MrBoggi/3d-boats/projects/01-21ft-rib/image.png

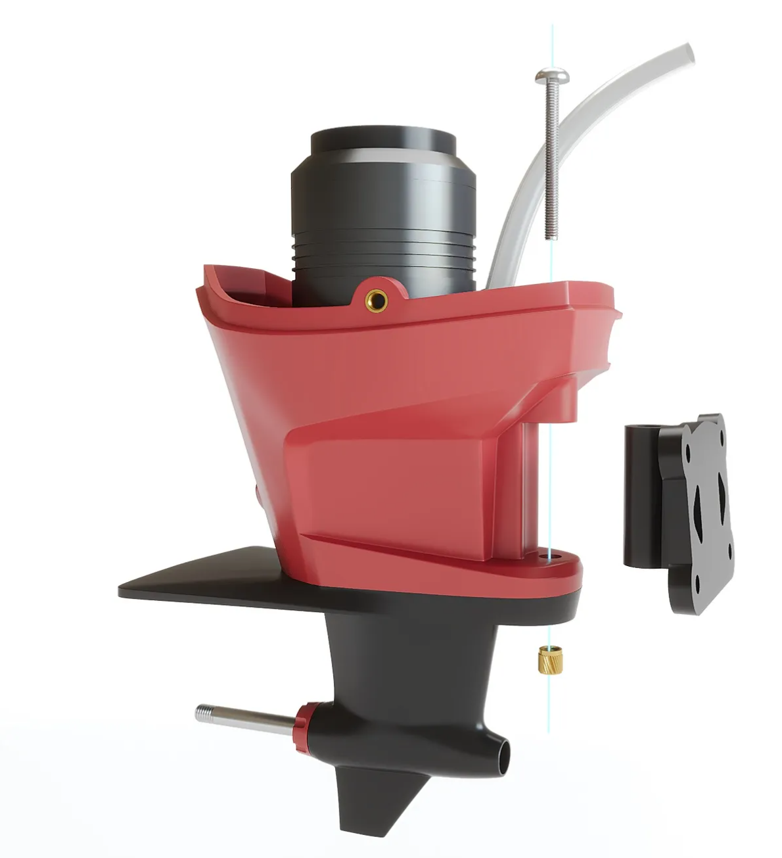
projects/01-21ft-rib/image.png
