MrBoggi/3d-boats/projects/02-21ft-rib-trailer/png/review_bogie_travel.png

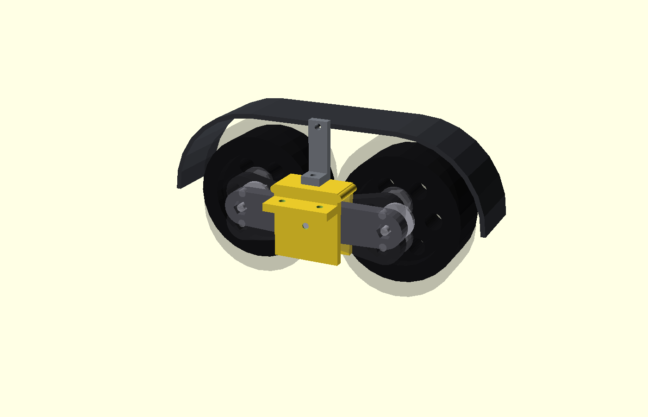
projects/02-21ft-rib-trailer/png/review_bogie_travel.png
