MrBoggi/3d-boats/projects/02-21ft-rib-trailer/png/review_bow_stop_pivot.png

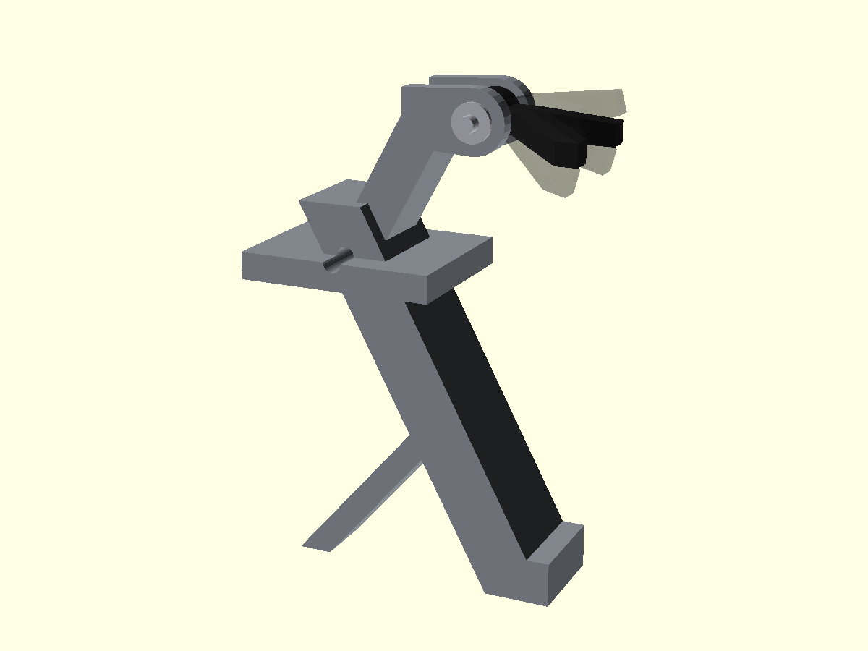
projects/02-21ft-rib-trailer/png/review_bow_stop_pivot.png
