MrBoggi/3d-boats/projects/02-21ft-rib-trailer/png/review_service_rear.png

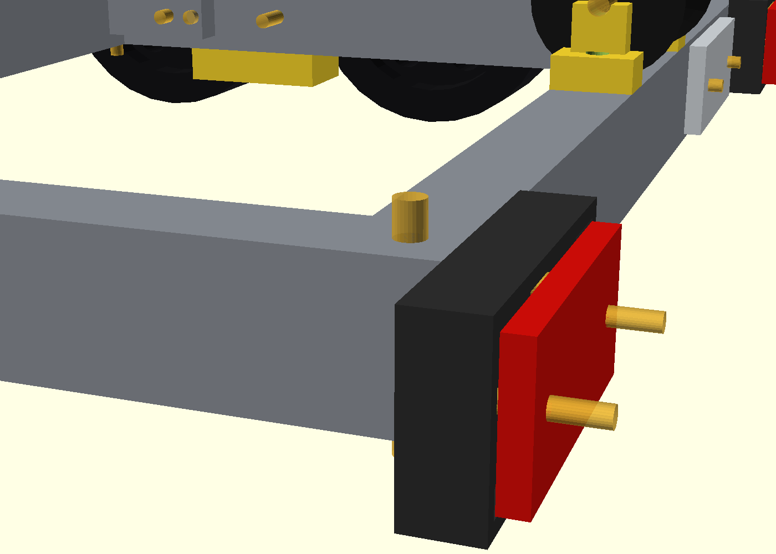
projects/02-21ft-rib-trailer/png/review_service_rear.png
