MrBoggi/3d-boats/projects/02-21ft-rib-trailer/3mf/plates/trailer_petg_plate_04.3mf

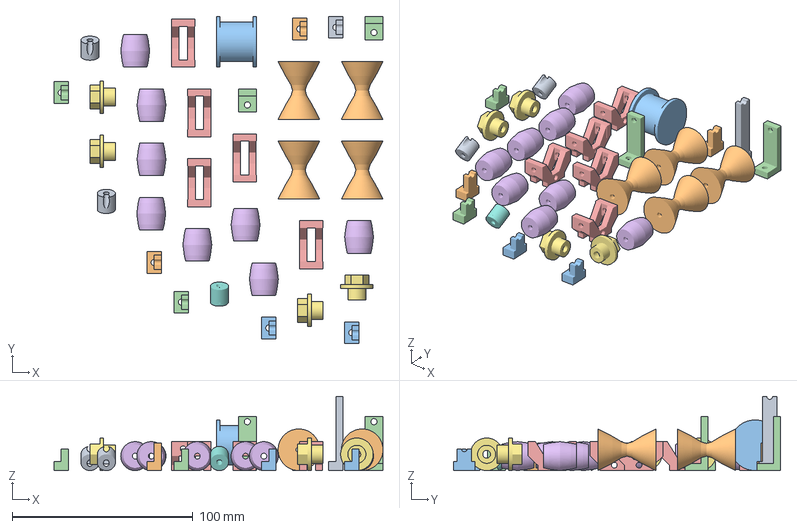
[picture p26: CAD file, 2026-08-22]
projects/02-21ft-rib-trailer/3mf/plates/trailer_petg_plate_04.3mf
181.9 x 180.8 x 41.0 mm
keel_roller_bracket_front.stl
keel_roller.stl x 4
winch_drum.stl
fender_mount_bracket.stl x 2
side_roller_wobble_holder.stl x 5
side_support_roller.stl x 8
wheel_hex_adapter.stl x 4
side_support_post_rear.stl
side_support_post_front.stl x 2
keel_roller_bracket_mid_front.stl x 2
keel_roller_bracket_mid_rear.stl x 2
keel_roller_bracket_rear.stl x 2
