MrBoggi/3d-boats/projects/02-21ft-rib-trailer/3mf/v_rail_joint_plate.3mf

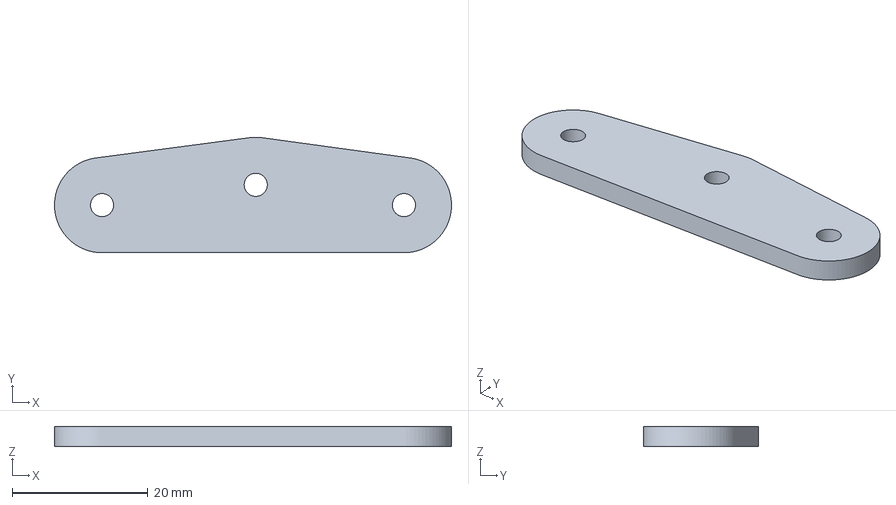
[picture p27: CAD file, 2026-08-17]
projects/02-21ft-rib-trailer/3mf/v_rail_joint_plate.3mf
58.4 x 17.0 x 3.00 mm
