MrBoggi/3d-boats/projects/01-21ft-rib/stl/bow_rail_port.stl

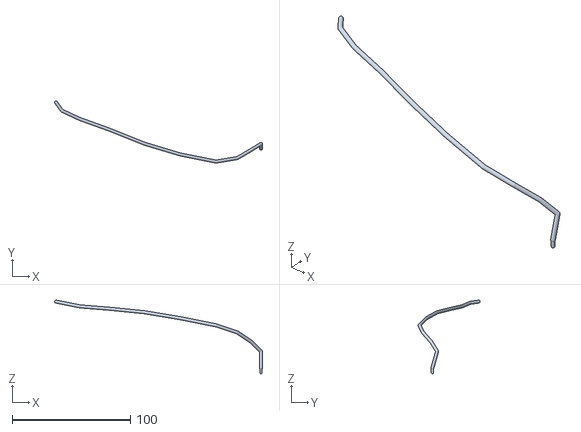
[picture p28: CAD file, 2026-08-11]
projects/01-21ft-rib/stl/bow_rail_port.stl
175.6 x 52.6 x 62.3
