MrBoggi/3d-boats/projects/02-21ft-rib-trailer/3mf/frame_rail_rear.3mf

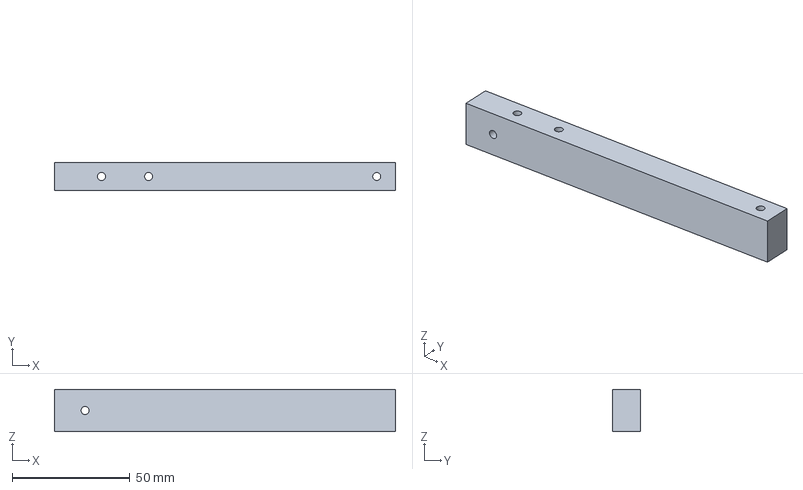
[picture p30: CAD file, 2026-08-17]
projects/02-21ft-rib-trailer/3mf/frame_rail_rear.3mf
145.0 x 12.0 x 18.0 mm
