MrBoggi/3d-boats/projects/01-21ft-rib/stl/floor_aft_lid.stl

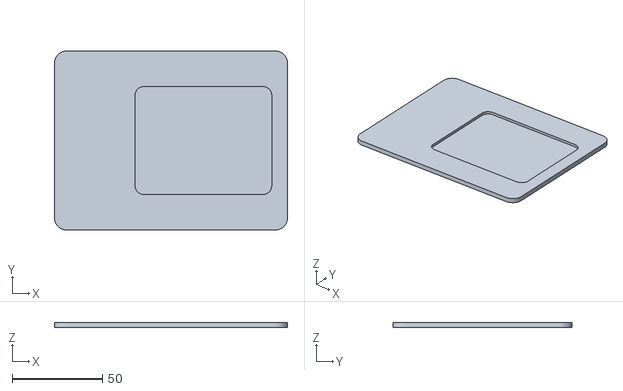
[picture p31: CAD file, 2026-08-11]
projects/01-21ft-rib/stl/floor_aft_lid.stl
129.4 x 99.4 x 3.00
