MrBoggi/3d-boats/projects/02-21ft-rib-trailer/3mf/plates/trailer_petg_plate_01.3mf

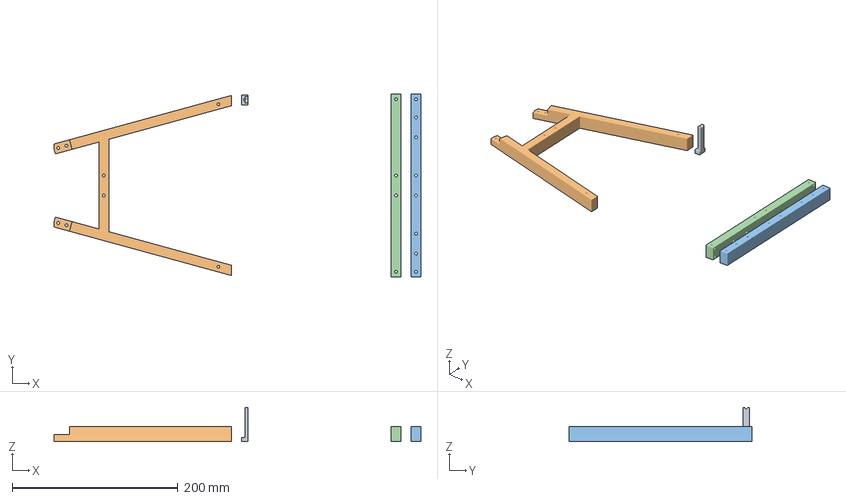
[picture p33: CAD file, 2026-08-22]
projects/02-21ft-rib-trailer/3mf/plates/trailer_petg_plate_01.3mf
442.2 x 220.0 x 41.0 mm
keel_roller_bracket_front.stl
drawbar_rear.stl
crossmember.stl
rear_accessory_crossmember.stl
