MrBoggi/3d-boats/projects/02-21ft-rib-trailer/3mf/rear_light_housing.3mf

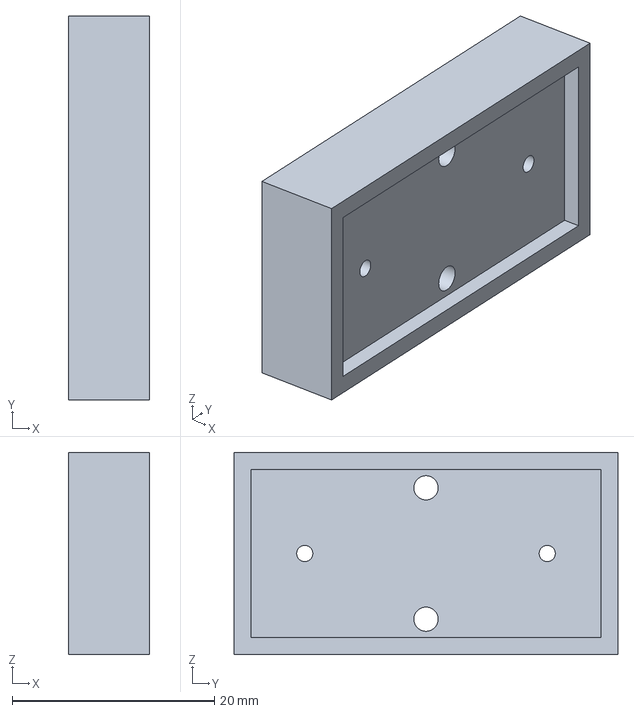
[picture p34: CAD file, 2026-08-17]
projects/02-21ft-rib-trailer/3mf/rear_light_housing.3mf
8.00 x 38.0 x 20.0 mm
