MrBoggi/3d-boats/projects/01-21ft-rib/stl/hull_mid.stl

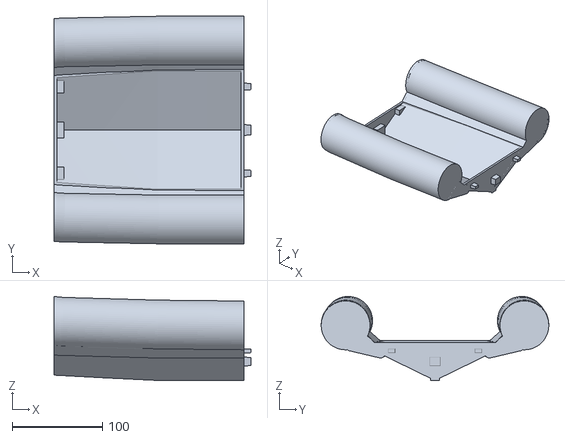
[picture p35: CAD file, 2026-08-11]
projects/01-21ft-rib/stl/hull_mid.stl
218.1 x 252.0 x 93.0
