MrBoggi/3d-boats/projects/02-21ft-rib-trailer/3mf/fit_tests/parts/fit_coupler_frame.3mf

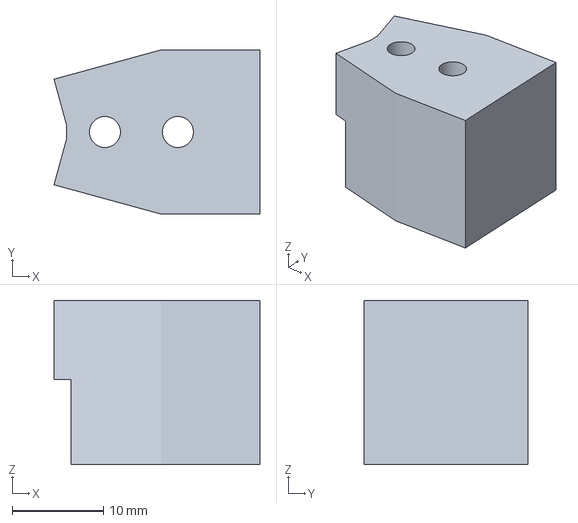
[picture p36: CAD file, 2026-08-22]
projects/02-21ft-rib-trailer/3mf/fit_tests/parts/fit_coupler_frame.3mf
22.6 x 18.0 x 18.0 mm
