MrBoggi/3d-boats/projects/02-21ft-rib-trailer/3mf/side_support_receiver.3mf

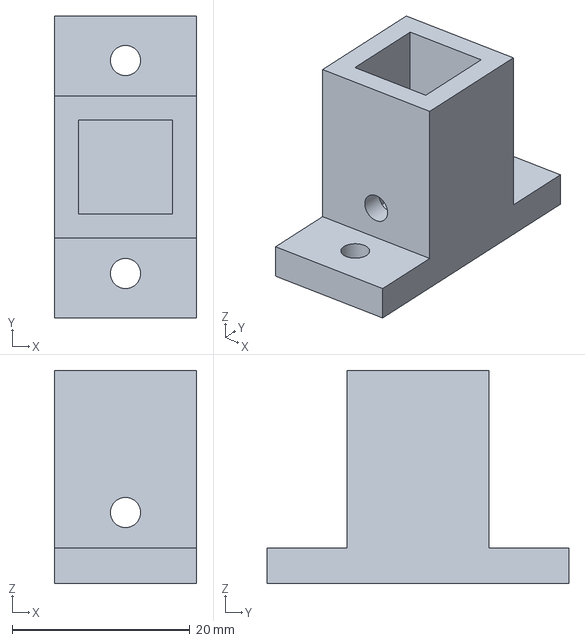
[picture p37: CAD file, 2026-08-17]
projects/02-21ft-rib-trailer/3mf/side_support_receiver.3mf
16.0 x 34.0 x 24.0 mm
