MrBoggi/3d-boats/projects/01-21ft-rib/stl/console.stl

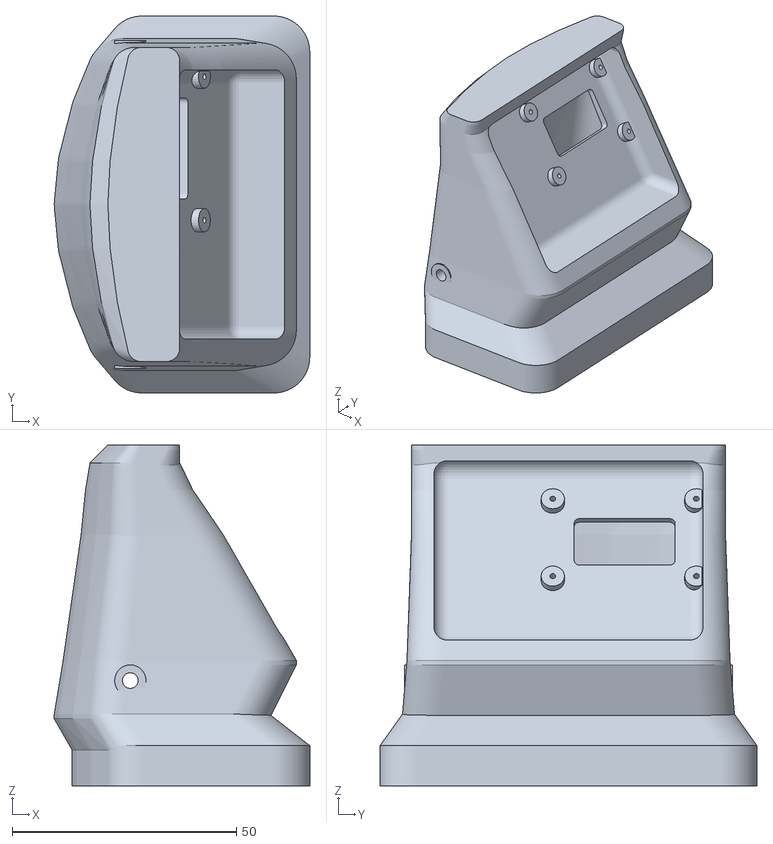
[picture p38: CAD file, 2026-08-11]
projects/01-21ft-rib/stl/console.stl
57.0 x 84.0 x 76.0
