MrBoggi/3d-boats/projects/02-21ft-rib-trailer/3mf/fit_tests/parts/fit_v_rear.3mf

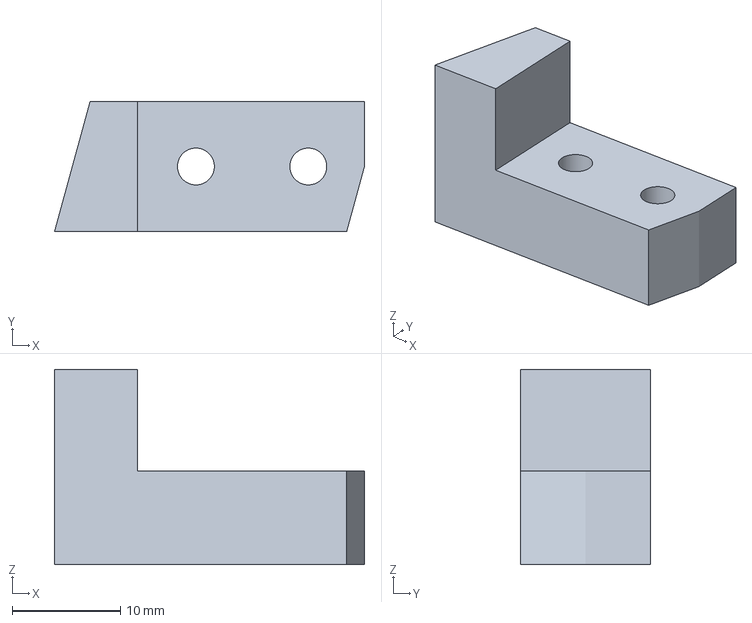
[picture p39: CAD file, 2026-08-22]
projects/02-21ft-rib-trailer/3mf/fit_tests/parts/fit_v_rear.3mf
28.6 x 12.0 x 18.0 mm
