MrBoggi/3d-boats/projects/02-21ft-rib-trailer/3mf/frame_rail_middle.3mf

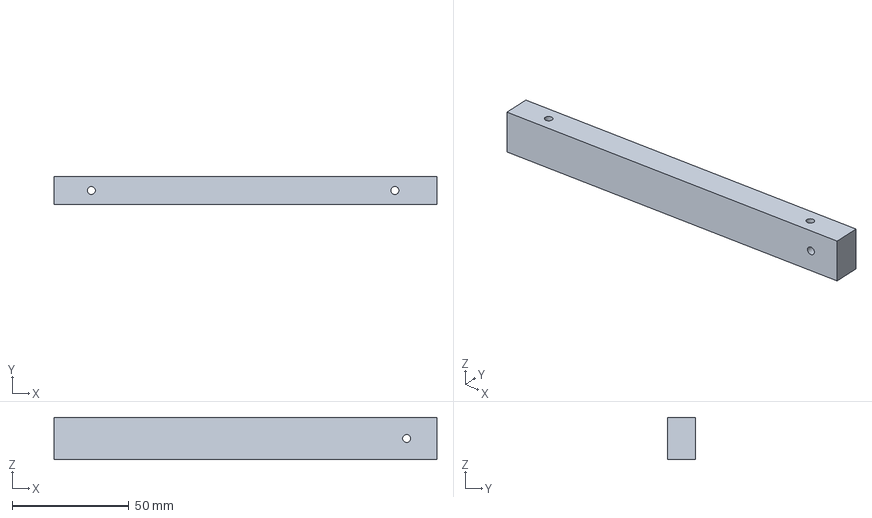
[picture p40: CAD file, 2026-08-17]
projects/02-21ft-rib-trailer/3mf/frame_rail_middle.3mf
164.0 x 12.0 x 18.0 mm
