MrBoggi/3d-boats/projects/01-21ft-rib/stl/console_oled_retainer.stl

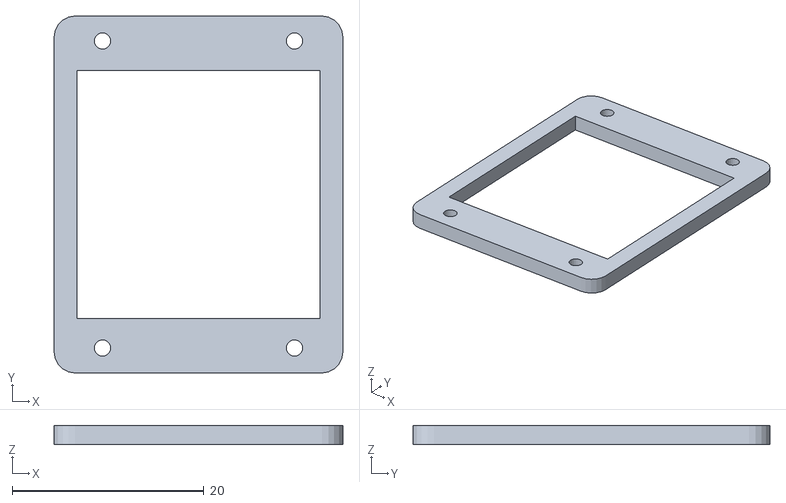
[picture p41: CAD file, 2026-08-11]
projects/01-21ft-rib/stl/console_oled_retainer.stl
30.1 x 37.2 x 2.00
