MrBoggi/3d-boats/projects/02-21ft-rib-trailer/3mf/fit_tests/parts/fit_side_post_head.3mf

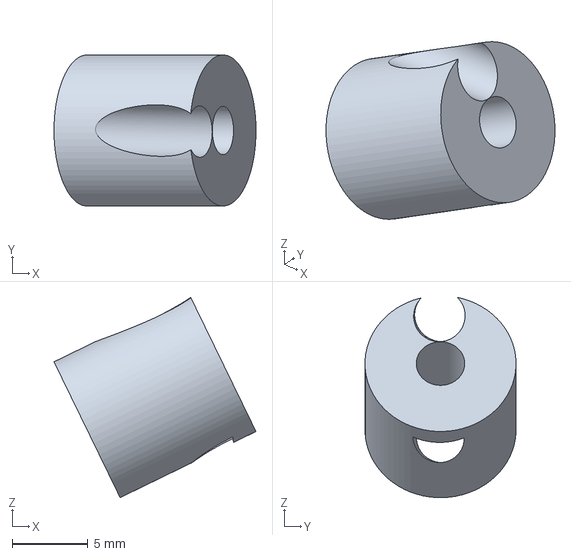
[picture p42: CAD file, 2026-08-22]
projects/02-21ft-rib-trailer/3mf/fit_tests/parts/fit_side_post_head.3mf
13.4 x 10.00 x 13.3 mm
