MrBoggi/3d-boats/projects/02-21ft-rib-trailer/3mf/tandem_fender.3mf

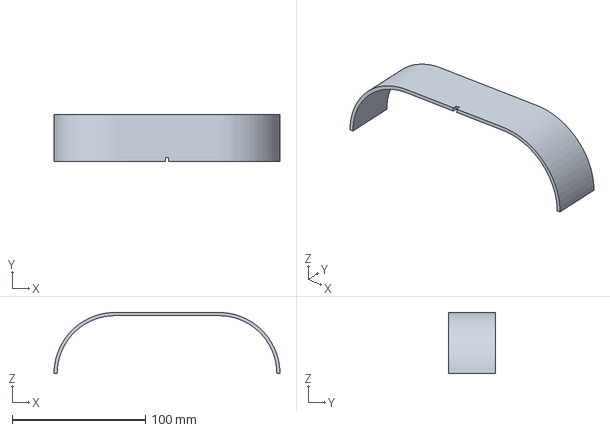
[picture p43: CAD file, 2026-08-17]
projects/02-21ft-rib-trailer/3mf/tandem_fender.3mf
169.8 x 35.1 x 45.9 mm
