MrBoggi/3d-boats/projects/02-21ft-rib-trailer/3mf/fit_tests/parts/bogie_mount.3mf

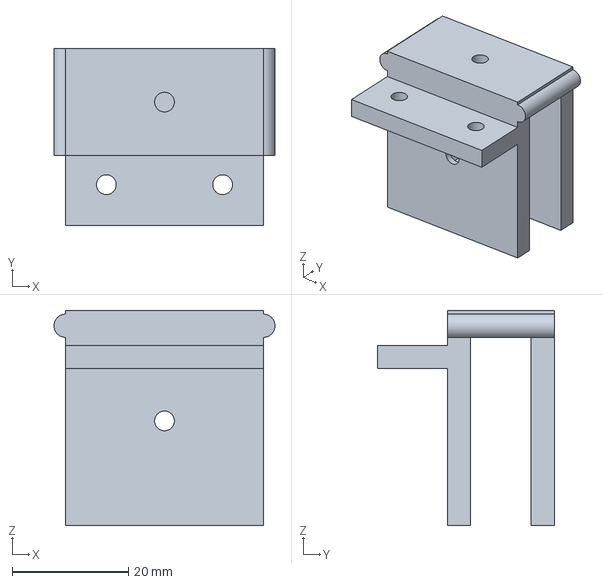
[picture p44: CAD file, 2026-08-22]
projects/02-21ft-rib-trailer/3mf/fit_tests/parts/bogie_mount.3mf
38.0 x 30.4 x 37.0 mm
