MrBoggi/3d-boats/projects/02-21ft-rib-trailer/3mf/rear_light_lens.3mf

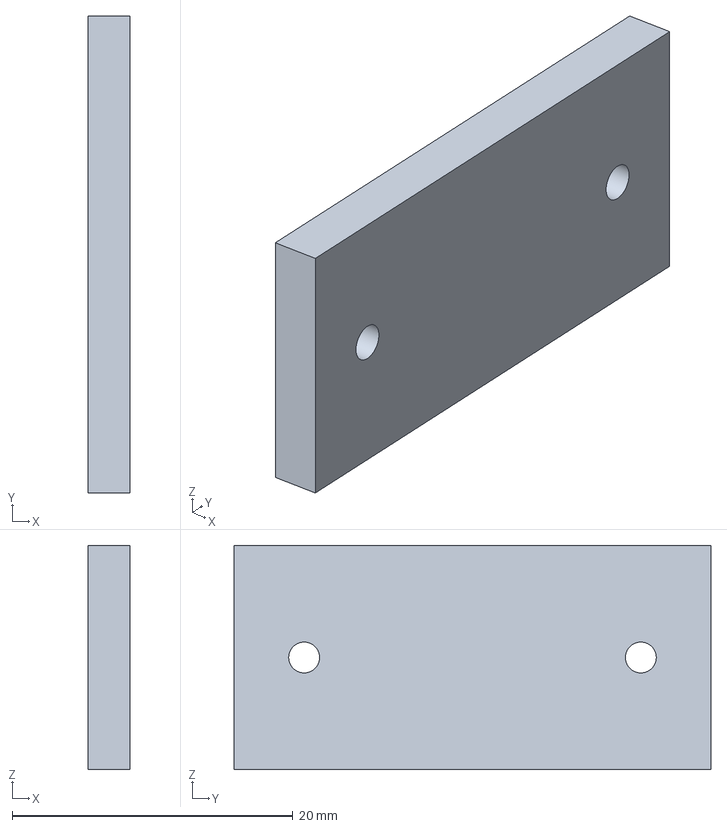
[picture p45: CAD file, 2026-08-17]
projects/02-21ft-rib-trailer/3mf/rear_light_lens.3mf
3.00 x 34.0 x 16.0 mm
