MrBoggi/3d-boats/projects/01-21ft-rib/stl/aft_bench_cushion.stl

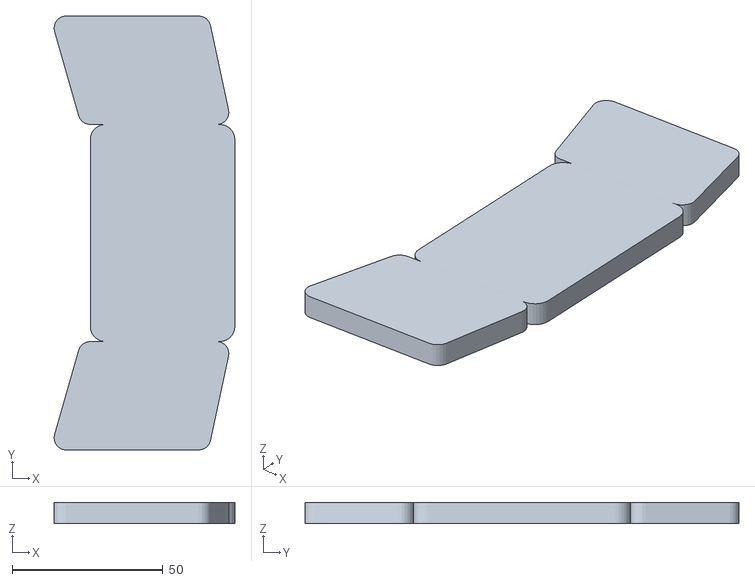
[picture p46: CAD file, 2026-08-11]
projects/01-21ft-rib/stl/aft_bench_cushion.stl
60.0 x 144.0 x 7.00
