MrBoggi/3d-boats/projects/02-21ft-rib-trailer/3mf/winch_tower_body.3mf

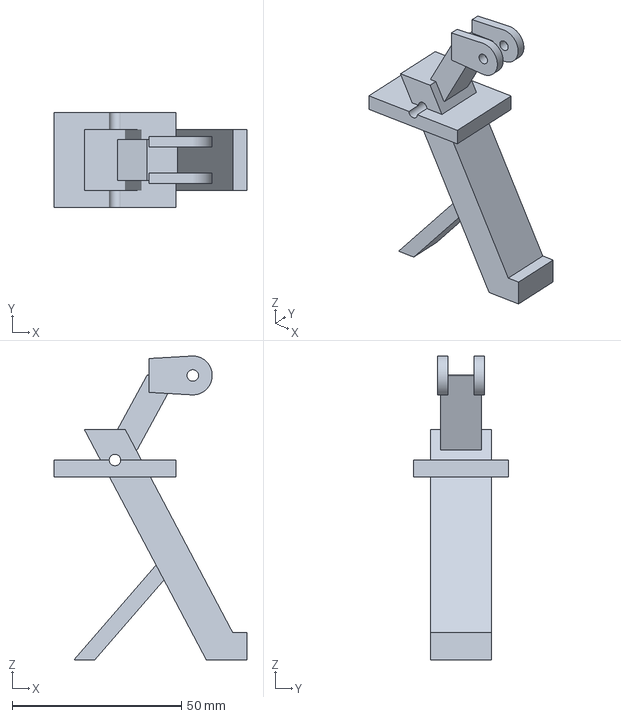
[picture p47: CAD file, 2026-08-17]
projects/02-21ft-rib-trailer/3mf/winch_tower_body.3mf
57.0 x 28.0 x 89.9 mm
