MrBoggi/3d-boats/projects/01-21ft-rib/stl/helm_bench_frame_starboard.stl

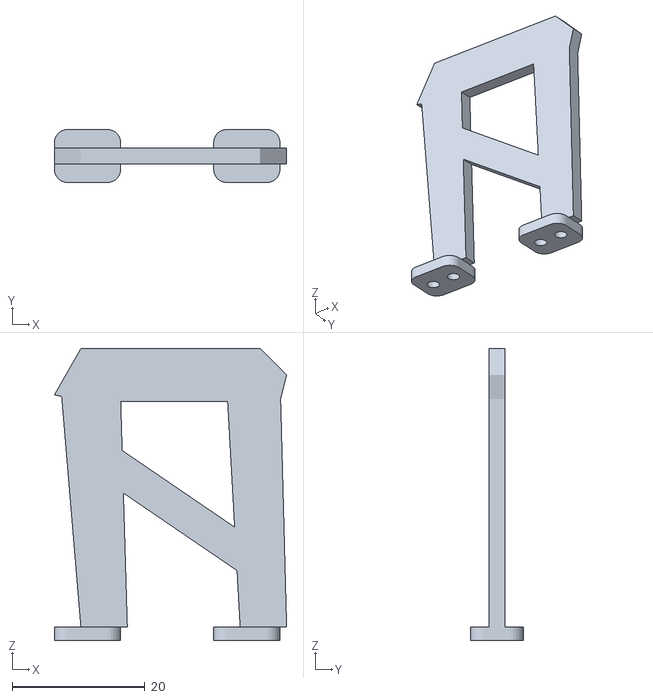
[picture p48: CAD file, 2026-08-11]
projects/01-21ft-rib/stl/helm_bench_frame_starboard.stl
35.0 x 8.00 x 44.0
