MrBoggi/3d-boats/projects/02-21ft-rib-trailer/3mf/crossmember.3mf

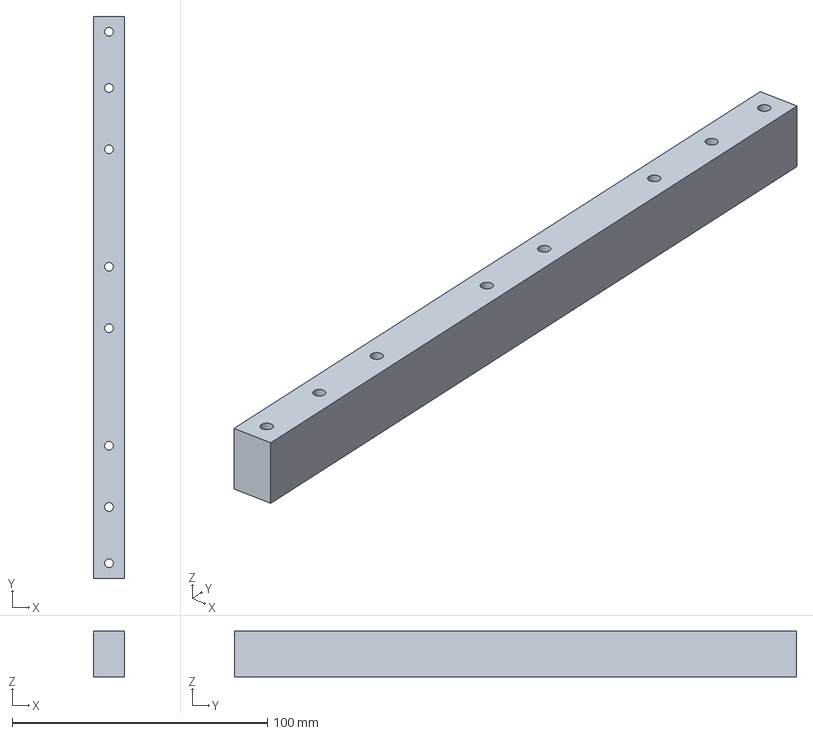
[picture p49: CAD file, 2026-08-17]
projects/02-21ft-rib-trailer/3mf/crossmember.3mf
12.0 x 220.0 x 18.0 mm
