MrBoggi/3d-boats/projects/02-21ft-rib-trailer/3mf/fit_tests/parts/coupler_mount_adapter.3mf

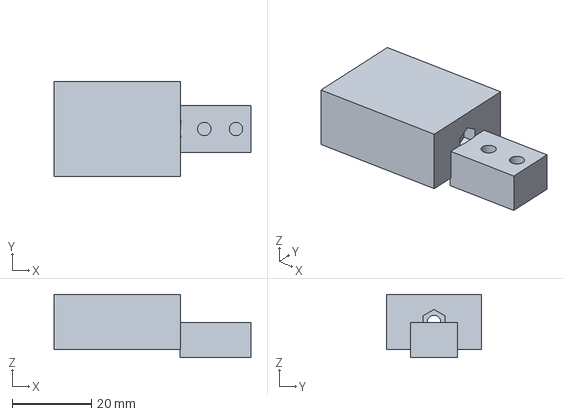
[picture p50: CAD file, 2026-08-22]
projects/02-21ft-rib-trailer/3mf/fit_tests/parts/coupler_mount_adapter.3mf
49.8 x 24.0 x 16.0 mm
