MrBoggi/3d-boats/projects/01-21ft-rib/stl/ladder.stl

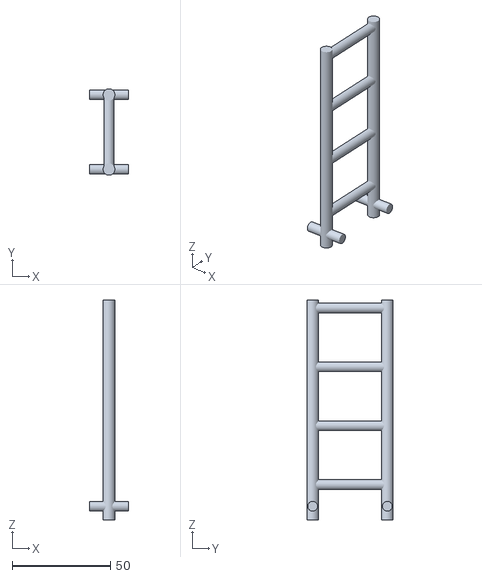
[picture p51: CAD file, 2026-08-11]
projects/01-21ft-rib/stl/ladder.stl
20.0 x 44.0 x 112.0
