MrBoggi/3d-boats/projects/02-21ft-rib-trailer/3mf/crossmember_joint_plate_rear.3mf

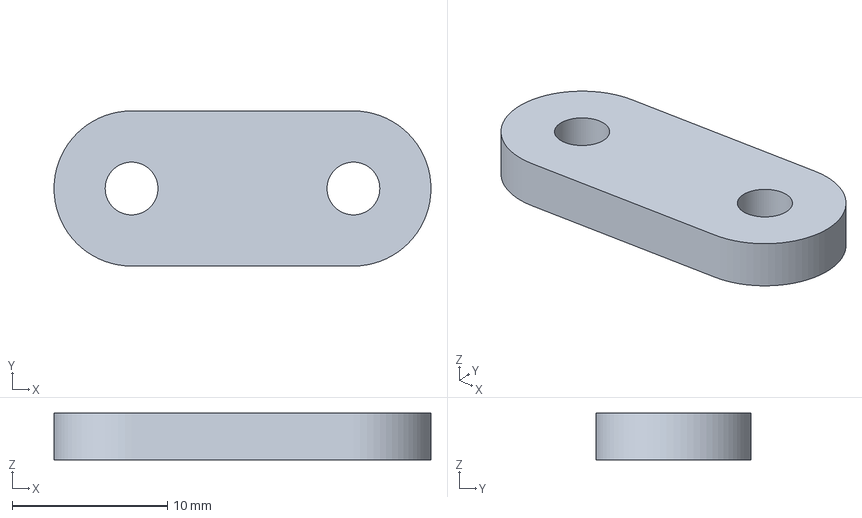
[picture p52: CAD file, 2026-08-17]
projects/02-21ft-rib-trailer/3mf/crossmember_joint_plate_rear.3mf
24.3 x 10.0 x 3.00 mm
