MrBoggi/3d-boats/projects/01-21ft-rib/stl/outboard_xl_adapter.stl

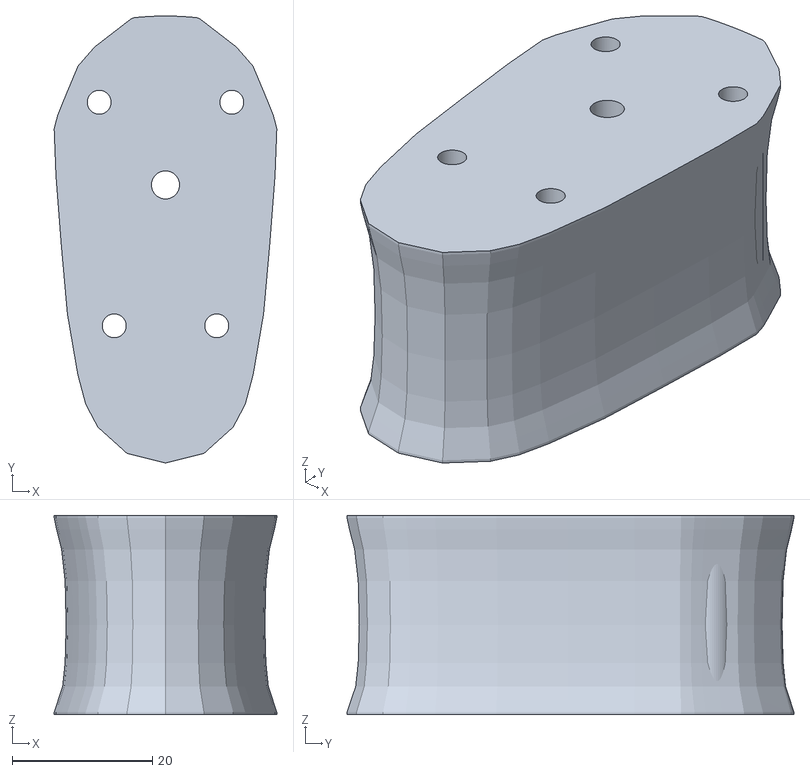
[picture p53: CAD file, 2026-08-11]
projects/01-21ft-rib/stl/outboard_xl_adapter.stl
31.7 x 63.7 x 28.4
