MrBoggi/3d-boats/projects/02-21ft-rib-trailer/3mf/drawbar_rear.3mf

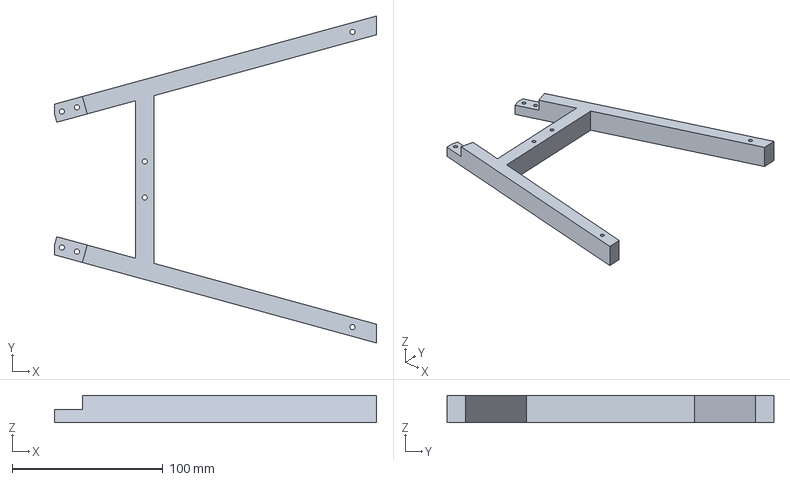
[picture p54: CAD file, 2026-08-17]
projects/02-21ft-rib-trailer/3mf/drawbar_rear.3mf
214.0 x 217.2 x 18.0 mm
