MrBoggi/3d-boats/projects/01-21ft-rib/stl/windshield_frame.stl

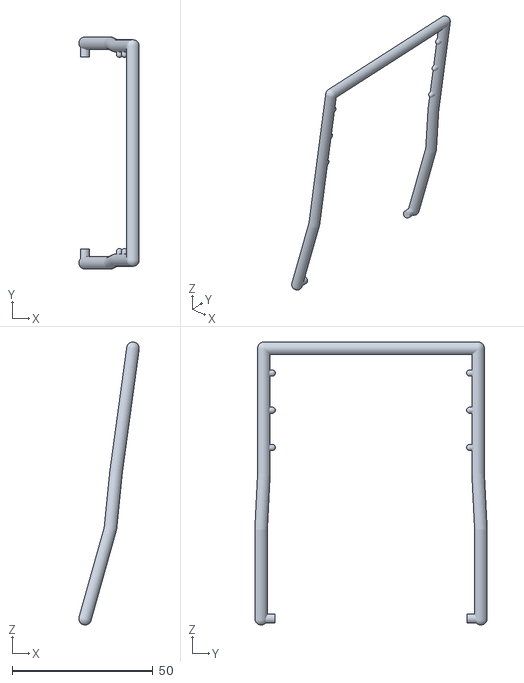
[picture p56: CAD file, 2026-08-11]
projects/01-21ft-rib/stl/windshield_frame.stl
21.5 x 82.5 x 100.5
