MrBoggi/3d-boats/projects/02-21ft-rib-trailer/3mf/fit_tests/parts/splice_plate.3mf

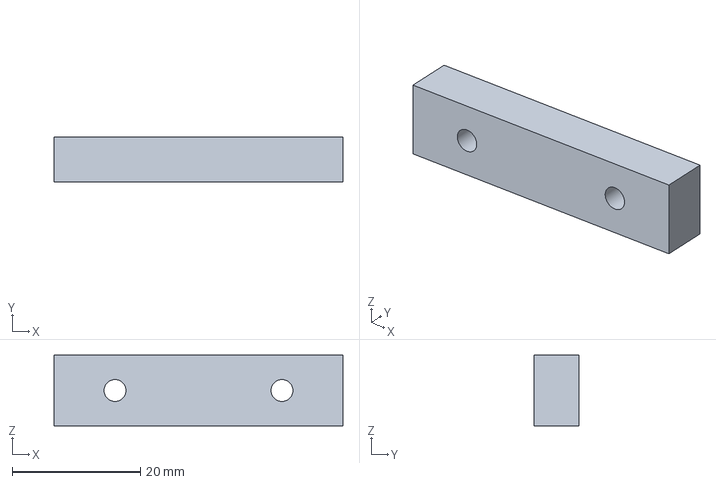
[picture p57: CAD file, 2026-08-22]
projects/02-21ft-rib-trailer/3mf/fit_tests/parts/splice_plate.3mf
45.0 x 7.00 x 11.0 mm
