MrBoggi/3d-boats/projects/01-21ft-rib/stl/aft_bench_backrest.stl

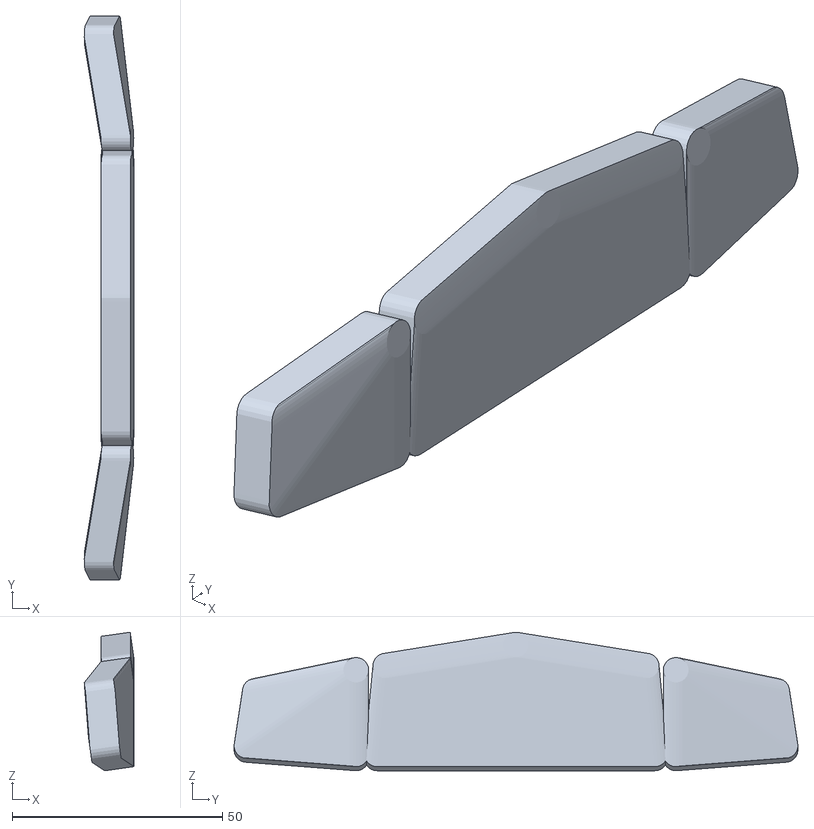
[picture p58: CAD file, 2026-08-11]
projects/01-21ft-rib/stl/aft_bench_backrest.stl
11.8 x 134.0 x 32.9
