MrBoggi/3d-boats/projects/02-21ft-rib-trailer/3mf/fit_tests/parts/fit_rear_crossmember.3mf

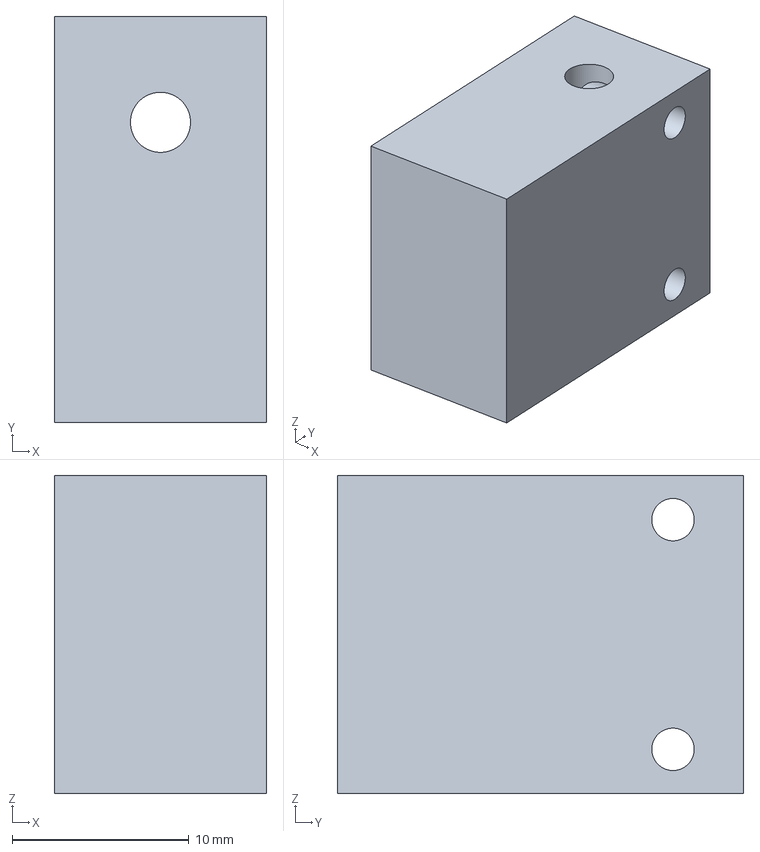
[picture p59: CAD file, 2026-08-22]
projects/02-21ft-rib-trailer/3mf/fit_tests/parts/fit_rear_crossmember.3mf
12.0 x 23.0 x 18.0 mm
