MrBoggi/3d-boats/projects/02-21ft-rib-trailer/3mf/side_roller_wobble_holder.3mf

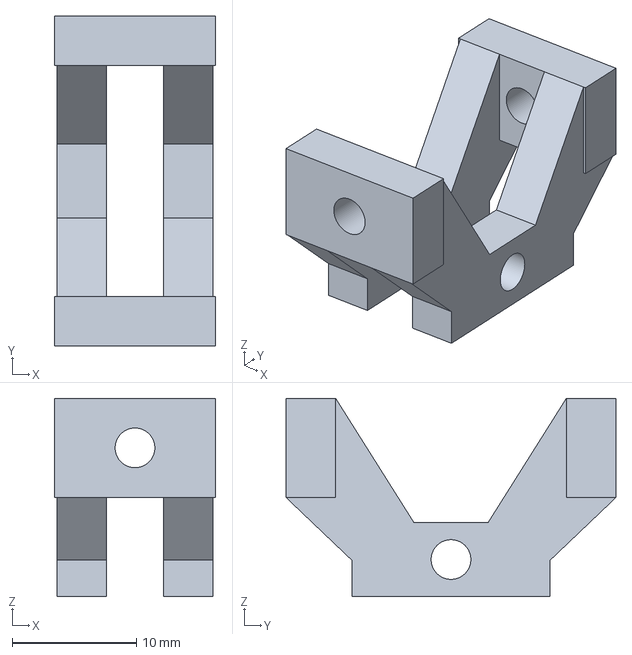
[picture p60: CAD file, 2026-08-17]
projects/02-21ft-rib-trailer/3mf/side_roller_wobble_holder.3mf
13.0 x 26.6 x 16.0 mm
