MrBoggi/3d-boats/projects/01-21ft-rib/stl/hull_bow.stl

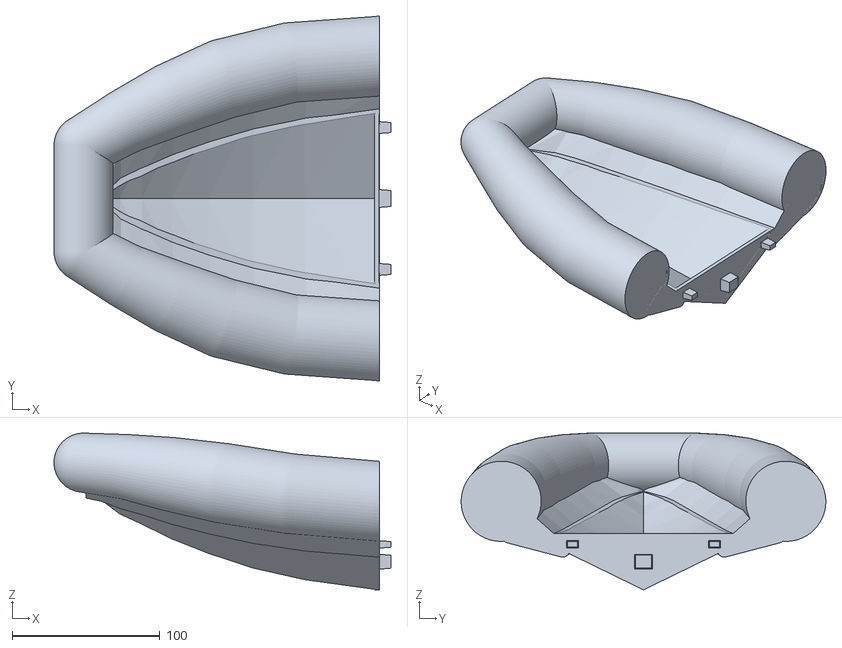
[picture p61: CAD file, 2026-08-11]
projects/01-21ft-rib/stl/hull_bow.stl
228.0 x 246.7 x 106.1
