MrBoggi/3d-boats/projects/02-21ft-rib-trailer/3mf/wheel_hex_adapter.3mf

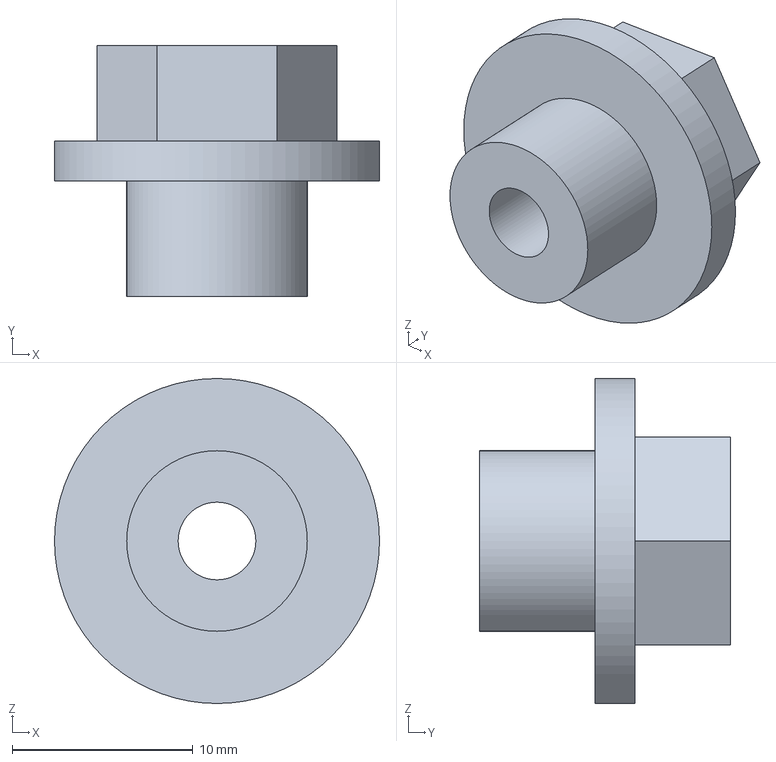
[picture p62: CAD file, 2026-08-17]
projects/02-21ft-rib-trailer/3mf/wheel_hex_adapter.3mf
18.0 x 13.9 x 18.0 mm
