MrBoggi/3d-boats/projects/01-21ft-rib/stl/helm_bench_side_rails.stl

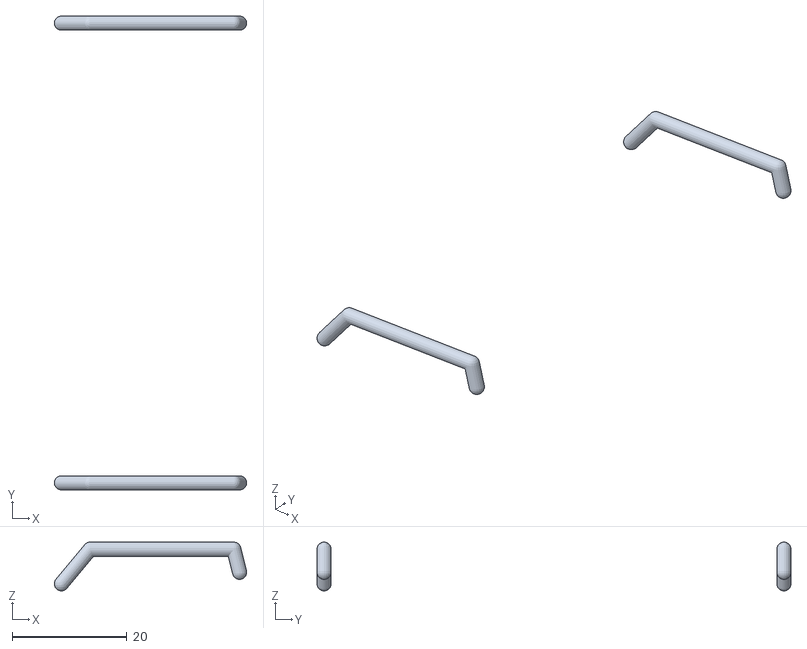
[picture p63: CAD file, 2026-08-11]
projects/01-21ft-rib/stl/helm_bench_side_rails.stl
33.5 x 82.5 x 8.47
