MrBoggi/3d-boats/projects/01-21ft-rib/stl/helm_bench_cushion.stl

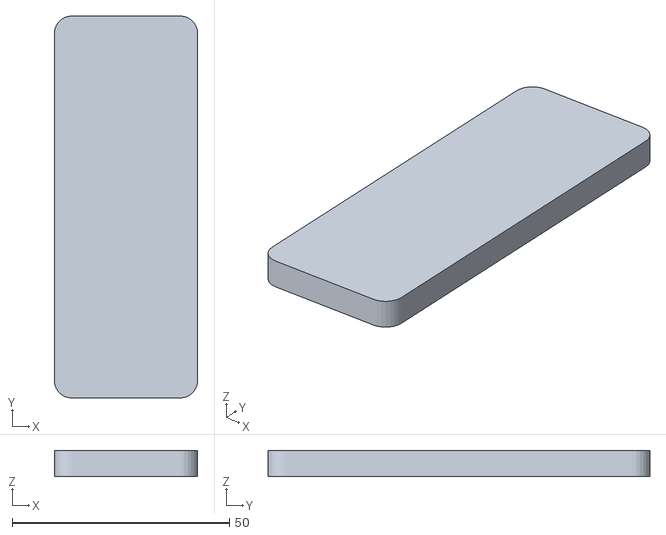
[picture p64: CAD file, 2026-08-11]
projects/01-21ft-rib/stl/helm_bench_cushion.stl
33.0 x 88.0 x 6.00
