MrBoggi/3d-boats/projects/02-21ft-rib-trailer/3mf/bogie_arm.3mf

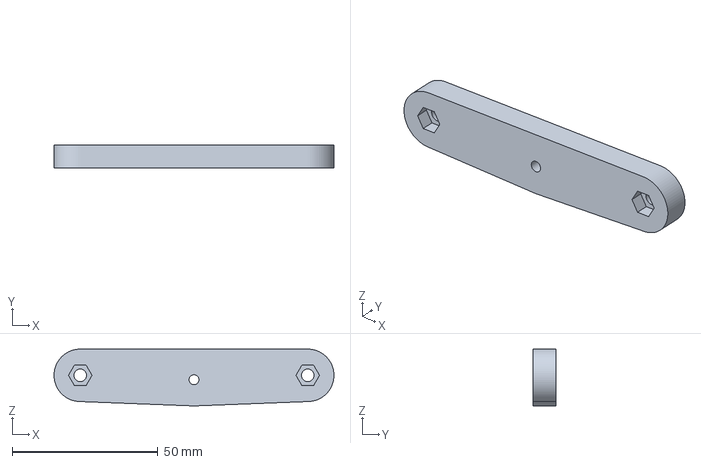
[picture p65: CAD file, 2026-08-17]
projects/02-21ft-rib-trailer/3mf/bogie_arm.3mf
96.0 x 8.00 x 19.5 mm
