MrBoggi/3d-boats/projects/01-21ft-rib/stl/floor_battery_lid.stl

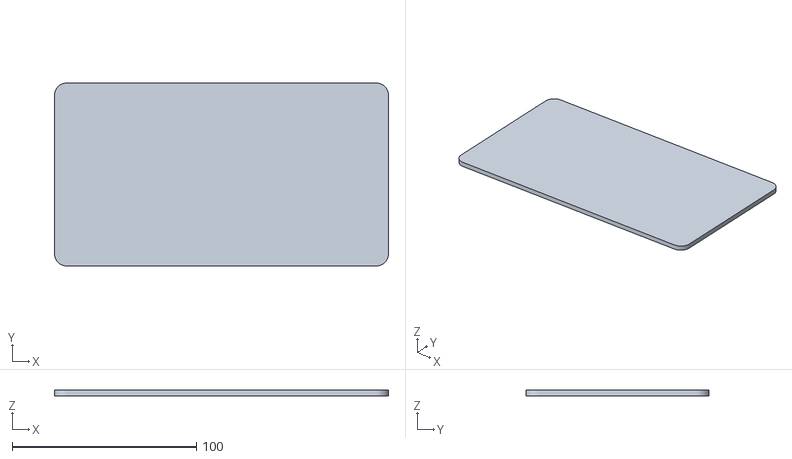
[picture p66: CAD file, 2026-08-11]
projects/01-21ft-rib/stl/floor_battery_lid.stl
181.4 x 99.4 x 3.00
