MrBoggi/3d-boats/projects/02-21ft-rib-trailer/3mf/fender_mount_bracket.3mf

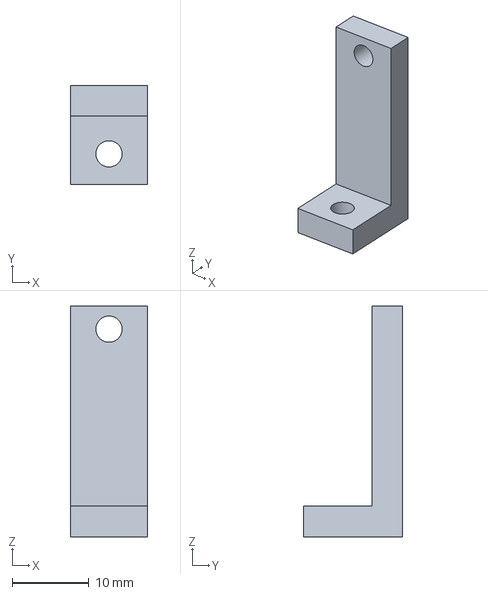
[picture p67: CAD file, 2026-08-17]
projects/02-21ft-rib-trailer/3mf/fender_mount_bracket.3mf
10.0 x 12.9 x 30.0 mm
