MrBoggi/3d-boats/projects/01-21ft-rib/stl/cockpit_floor_fixed.stl

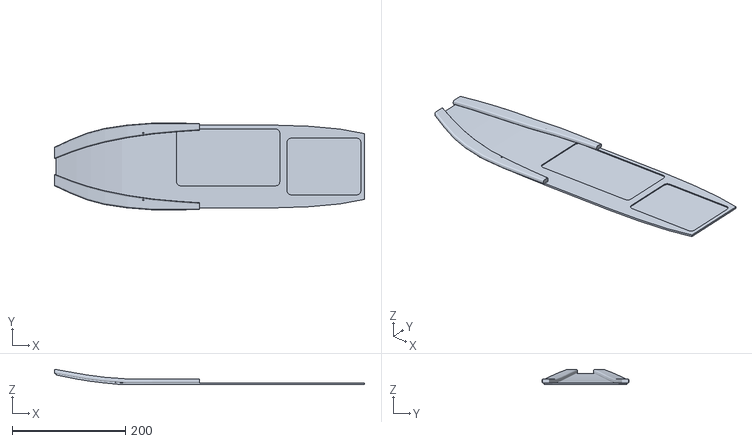
[picture p68: CAD file, 2026-08-11]
projects/01-21ft-rib/stl/cockpit_floor_fixed.stl
547.0 x 153.0 x 27.0
