MrBoggi/3d-boats/projects/01-21ft-rib/stl/hull_stern.stl

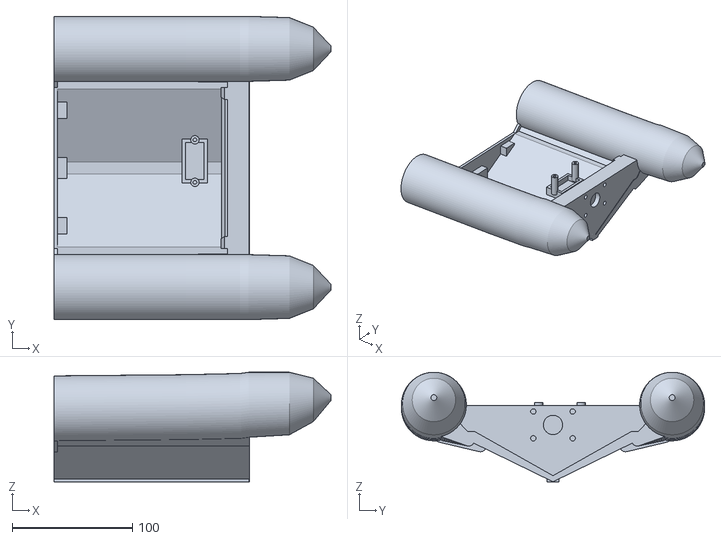
[picture p69: CAD file, 2026-08-11]
projects/01-21ft-rib/stl/hull_stern.stl
230.2 x 252.0 x 91.0
