MrBoggi/3d-boats/projects/02-21ft-rib-trailer/3mf/crossmember_mid.3mf

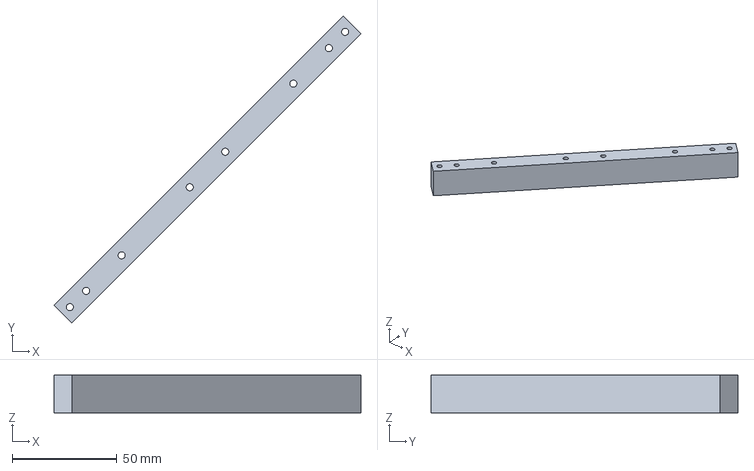
[picture p70: CAD file, 2026-08-17]
projects/02-21ft-rib-trailer/3mf/crossmember_mid.3mf
146.7 x 146.7 x 18.0 mm
