MrBoggi/3d-boats/projects/01-21ft-rib/stl/bow_anchor_roller.stl

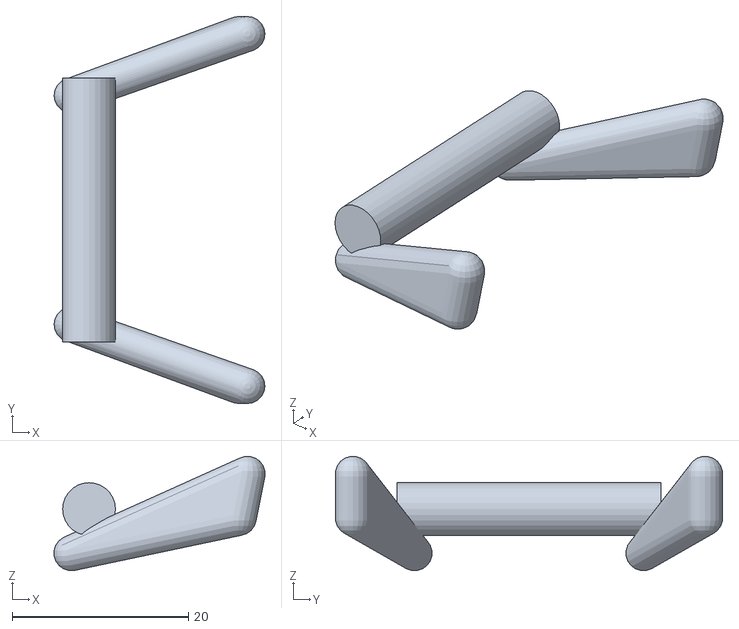
[picture p71: CAD file, 2026-08-11]
projects/01-21ft-rib/stl/bow_anchor_roller.stl
24.0 x 44.0 x 12.9
