MrBoggi/3d-boats/projects/02-21ft-rib-trailer/3mf/winch_drum.3mf

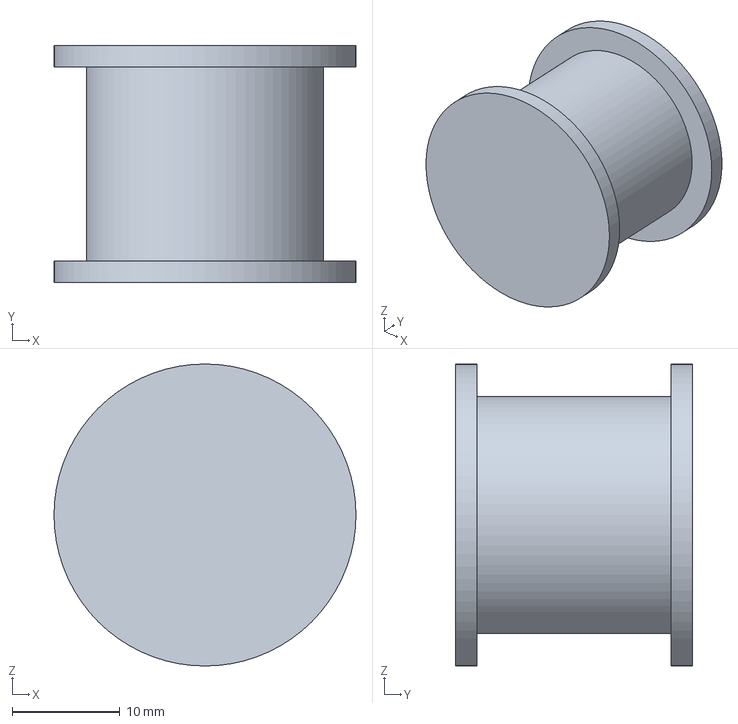
[picture p72: CAD file, 2026-08-17]
projects/02-21ft-rib-trailer/3mf/winch_drum.3mf
28.0 x 22.0 x 28.0 mm
