MrBoggi/3d-boats/projects/01-21ft-rib/stl/bow_cushion.stl

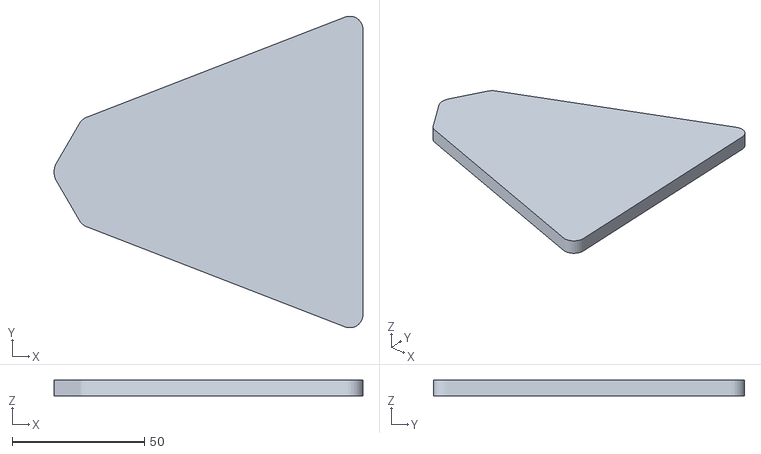
[picture p73: CAD file, 2026-08-11]
projects/01-21ft-rib/stl/bow_cushion.stl
117.0 x 117.9 x 6.00
