MrBoggi/3d-boats/projects/01-21ft-rib/stl/aft_bench_seat_support.stl

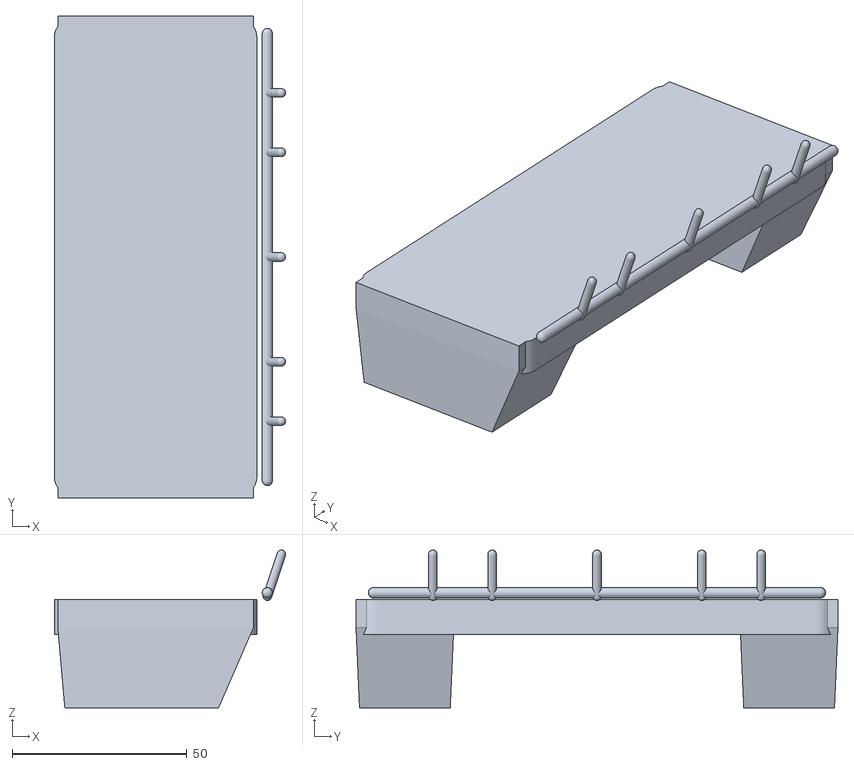
[picture p75: CAD file, 2026-08-11]
projects/01-21ft-rib/stl/aft_bench_seat_support.stl
66.2 x 138.0 x 45.2
