MrBoggi/3d-boats/projects/02-21ft-rib-trailer/3mf/keel_roller_bracket_front.3mf

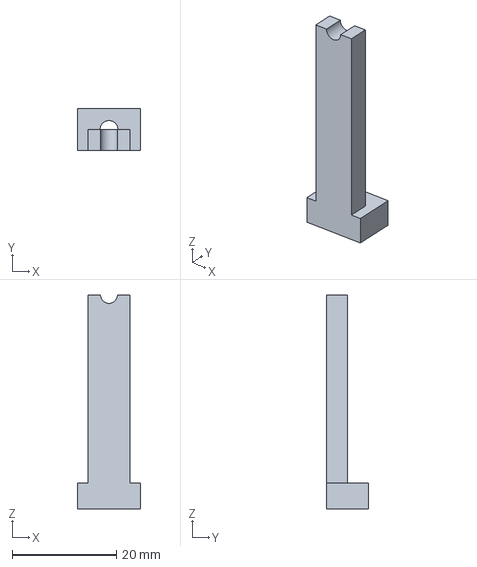
[picture p76: CAD file, 2026-08-17]
projects/02-21ft-rib-trailer/3mf/keel_roller_bracket_front.3mf
12.0 x 8.00 x 41.0 mm
