MrBoggi/3d-boats/projects/02-21ft-rib-trailer/3mf/winch_crank.3mf

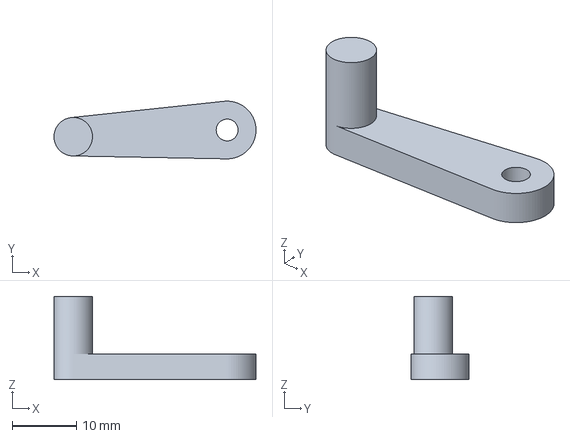
[picture p77: CAD file, 2026-08-17]
projects/02-21ft-rib-trailer/3mf/winch_crank.3mf
31.5 x 8.99 x 13.0 mm
