MrBoggi/3d-boats/projects/02-21ft-rib-trailer/3mf/license_plate_holder.3mf

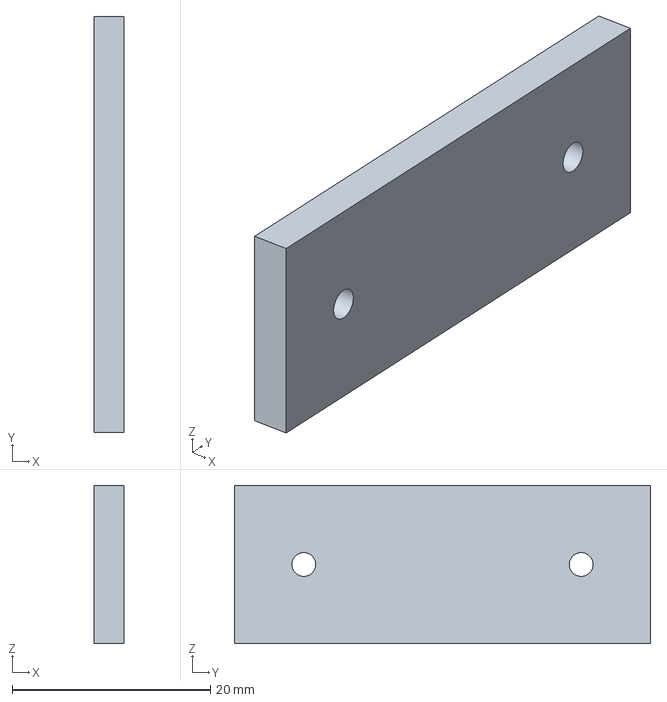
[picture p78: CAD file, 2026-08-17]
projects/02-21ft-rib-trailer/3mf/license_plate_holder.3mf
3.00 x 42.0 x 16.0 mm
