MrBoggi/3d-boats/projects/02-21ft-rib-trailer/3mf/side_support_roller.3mf

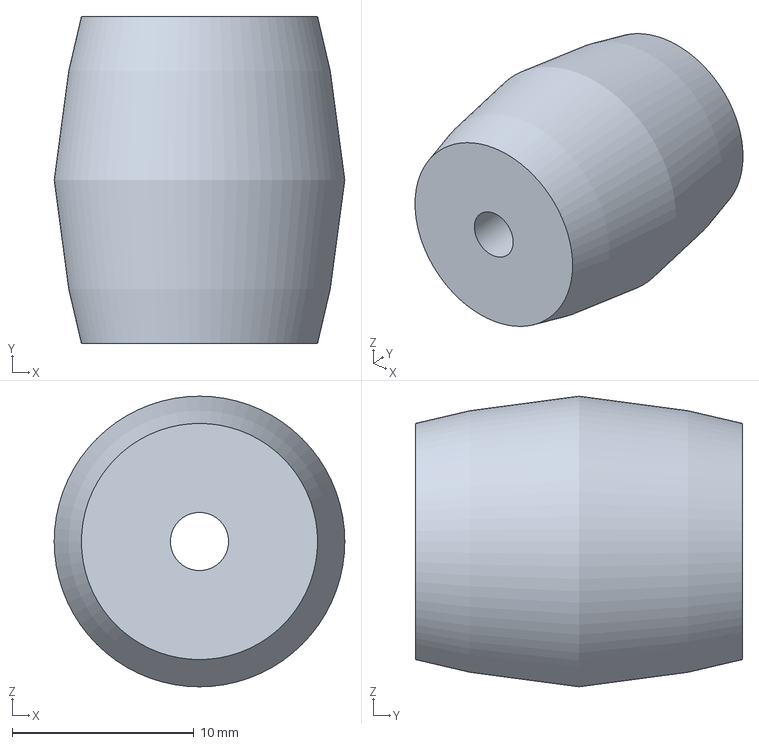
[picture p79: CAD file, 2026-08-17]
projects/02-21ft-rib-trailer/3mf/side_support_roller.3mf
16.0 x 18.0 x 16.0 mm
