MrBoggi/3d-boats/projects/02-21ft-rib-trailer/3mf/side_support_post_rear.3mf

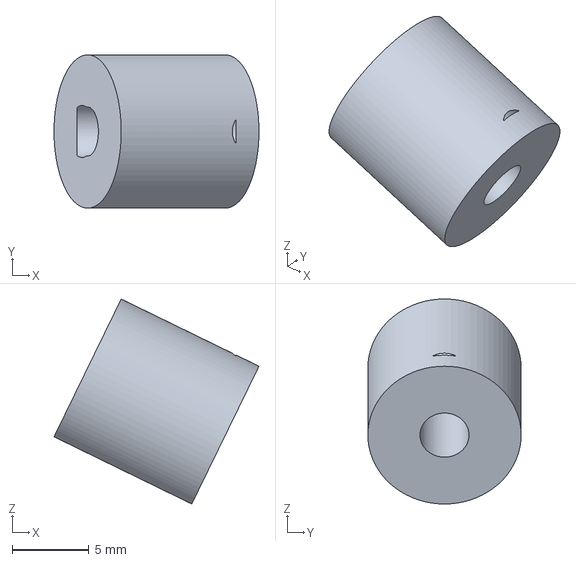
[picture p80: CAD file, 2026-08-17]
projects/02-21ft-rib-trailer/3mf/side_support_post_rear.3mf
13.4 x 10.00 x 13.4 mm
