MrBoggi/3d-boats/projects/02-21ft-rib-trailer/3mf/keel_roller.3mf

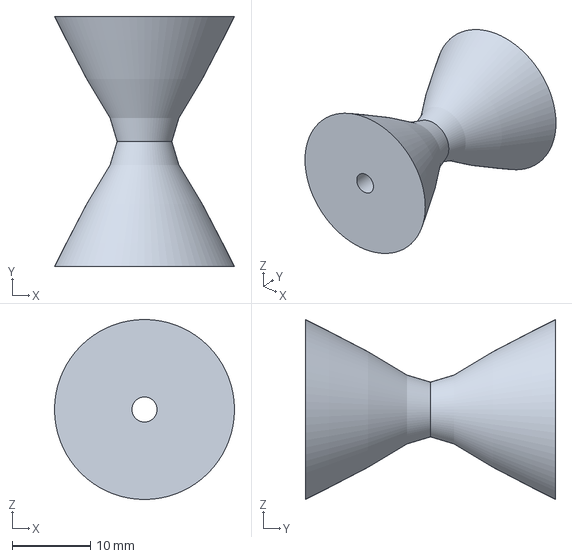
[picture p81: CAD file, 2026-08-17]
projects/02-21ft-rib-trailer/3mf/keel_roller.3mf
23.0 x 32.0 x 23.0 mm
