MrBoggi/3d-boats/projects/01-21ft-rib/png/assembly_side.png

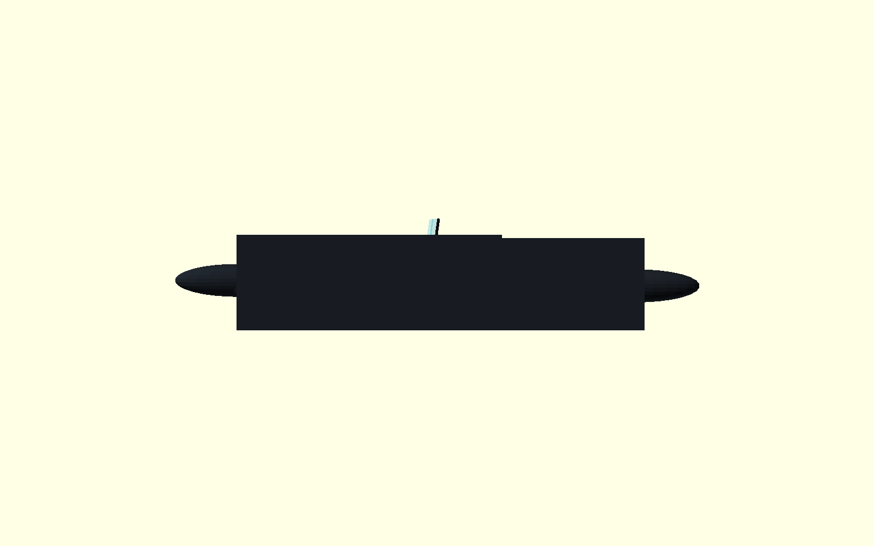
projects/01-21ft-rib/png/assembly_side.png
