MrBoggi/3d-boats/projects/02-21ft-rib-trailer/png/assembly_isometric.png

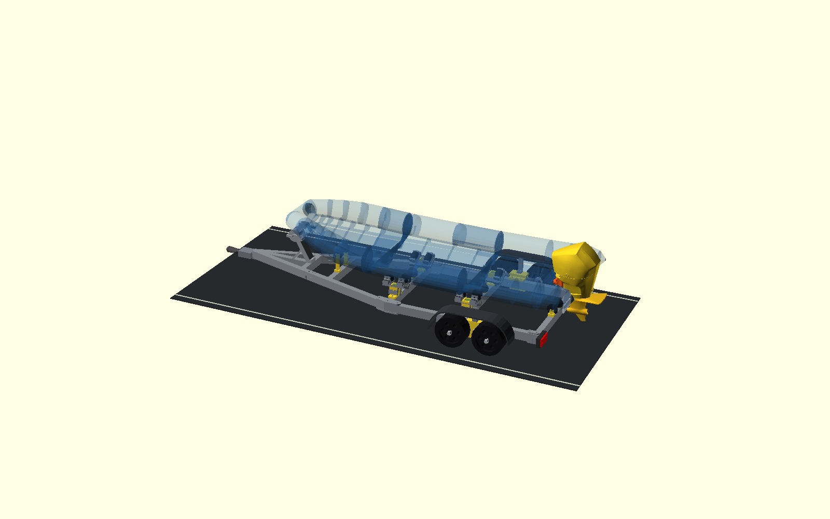
projects/02-21ft-rib-trailer/png/assembly_isometric.png
